JiGoRo1969/RL78G10_FootSensors/RL78G10_footsensors/cg_src/r_cg_cgc.h

/*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
* Copyright (C) 2012, 2019 Renesas Electronics Corporation. All rights reserved.
***********************************************************************************************************************/

/***********************************************************************************************************************
* File Name    : r_cg_cgc.h
* Version      : Code Generator for RL78/G10 V1.05.03.02 [20 Nov 2019]
* Device(s)    : R5F10Y47
* Tool-Chain   : CCRL
* Description  : This file implements device driver for CGC module.
* Creation Date: 2020/04/03
***********************************************************************************************************************/
#ifndef CGC_H
#define CGC_H

/***********************************************************************************************************************
Macro definitions (Register bit)
***********************************************************************************************************************/
/*
    Clock operation mode control register (CMC)
*/
/* High-speed system clock pin operation mode (EXCLK, OSCSEL) */
#define _C0_CGC_HISYS_PIN           (0xC0U)
#define _00_CGC_HISYS_PORT          (0x00U) /* X1, X2 as I/O port */
#define _40_CGC_HISYS_OSC           (0x40U) /* X1, X2 as crystal/ceramic resonator connection */
#define _80_CGC_HISYS_PORT1         (0x80U) /* X1, X2 as I/O port */
#define _C0_CGC_HISYS_EXT           (0xC0U) /* X1 as I/O port, X2 as external clock input */
/* Control of X1 high-speed system clock oscillation frequency (AMPH) */
#define _00_CGC_SYSOSC_UNDER10M     (0x00U) /* fX <= 10MHz */
#define _01_CGC_SYSOSC_OVER10M      (0x01U) /* fX > 10MHz */

/*
    Clock operation status control register (CSC)
*/
/* Control of high-speed system clock operation (MSTOP) */
#define _00_CGC_HISYS_OPER          (0x00U) /* X1 oscillator/external clock operating */
#define _80_CGC_HISYS_STOP          (0x80U) /* X1 oscillator/external clock stopped */
/* High-speed OCO operation (HIOSTOP) */
#define _00_CGC_HIO_OPER            (0x00U) /* high-speed OCO operating */
#define _01_CGC_HIO_STOP            (0x01U) /* high-speed OCO stopped */

/*
    Oscillation stabilization time counter status register (OSTC)
*/
/* Oscillation stabilization time status (MOST18 - MOST8) */
#define _00_CGC_OSCSTAB_STA0        (0x00U) /* < (2^8+16)/fX */
#define _80_CGC_OSCSTAB_STA8        (0x80U) /* (2^8+16)/fX */
#define _C0_CGC_OSCSTAB_STA9        (0xC0U) /* (2^9+16)/fX */
#define _E0_CGC_OSCSTAB_STA10       (0xE0U) /* (2^10+16)/fX */
#define _F0_CGC_OSCSTAB_STA11       (0xF0U) /* (2^11+16)/fX */
#define _F8_CGC_OSCSTAB_STA13       (0xF8U) /* (2^13+16)/fX */
#define _FC_CGC_OSCSTAB_STA15       (0xFCU) /* (2^15+16)/fX */
#define _FE_CGC_OSCSTAB_STA17       (0xFEU) /* (2^17+16)/fX */
#define _FF_CGC_OSCSTAB_STA18       (0xFFU) /* (2^18+16)/fX */

/*
    Oscillation stabilization time select register (OSTS)
*/
/* Oscillation stabilization time selection (OSTS2 - OSTS0) */
#define _00_CGC_OSCSTAB_SEL8        (0x00U) /* (2^8+16)/fX */
#define _01_CGC_OSCSTAB_SEL9        (0x01U) /* (2^9+16)/fX */
#define _02_CGC_OSCSTAB_SEL10       (0x02U) /* (2^10+16)/fX */
#define _03_CGC_OSCSTAB_SEL11       (0x03U) /* (2^11+16)/fX */
#define _04_CGC_OSCSTAB_SEL13       (0x04U) /* (2^13+16)/fX */
#define _05_CGC_OSCSTAB_SEL15       (0x05U) /* (2^15+16)/fX */
#define _06_CGC_OSCSTAB_SEL17       (0x06U) /* (2^17+16)/fX */
#define _07_CGC_OSCSTAB_SEL18       (0x07U) /* (2^18+16)/fX */

/*
    System clock control register (CKC)
*/
/* Status of main system clock fMAIN (MCS) */
#define _00_CGC_MAINCLK_HIO         (0x00U) /* high-speed OCO clock (fIH) */
#define _20_CGC_MAINCLK_HISYS       (0x20U) /* high-speed system clock (fMX) */
/* Selection of main system clock fMAIN (MCM0) */
#define _00_CGC_MAINCLK_SELHIO      (0x00U) /* high-speed OCO clock (fIH) */
#define _10_CGC_MAINCLK_SELHISYS    (0x10U) /* high-speed system clock (fMX) */

/*
    Operation speed mode control register (OSMC)
*/
/* Interval timer unit input clock supply (WUTMMCK0) */
#define _00_CGC_IT_CLK_NO           (0x00U) /* stops clock supply */
#define _10_CGC_IT_CLK_FIL          (0x10U) /* use fIL clcok */

/***********************************************************************************************************************
Macro definitions
***********************************************************************************************************************/

/***********************************************************************************************************************
Typedef definitions
***********************************************************************************************************************/
typedef enum
{
    HIOCLK, 
    SYSX1CLK, 
    SYSEXTCLK
} clock_mode_t;

/***********************************************************************************************************************
Global functions
***********************************************************************************************************************/
void R_CGC_Create(void);

/* Start user code for function. Do not edit comment generated here */
/* End user code. Do not edit comment generated here */
#endif
